jurekms/ModBusWaterMeter/src/waterMeter/timers.c

/*
 * timers.c
 *
 *  Created on: 22 wrz 2021
 *      Author: JUREK
 */


#include "timers.h"

/******************************************************************************************************************************************************
 *
 * GLOBAL VARIABLES
 *
 *******************************************************************************************************************************************************/

volatile 	TTimers			WM_TIMERS ;


/******************************************************************************************************************************************************
 *
 *initialize all timers store in WM_TIMERS GLOBAL VARIABLE
 *
 *@param	void
 *
 *@return	void
 *
 *******************************************************************************************************************************************************/

void wmTimersInit(void) {
	WM_TIMERS.LEDGreenTimer = 0;
	WM_TIMERS.LEDRedTimer = 0;
	WM_TIMERS.wmContinuousWaterFlowPeriodTimer = 0;
	WM_TIMERS.wmNoWaterFlowTimer = 0;
}
