jurekms/ModBusWaterMeter/src/waterMeter/timers.h

/*
 * timers.h
 *
 *  Created on: 22 wrz 2021
 *      Author: JUREK
 */

#ifndef SRC_WATERMETER_TIMERS_H_
#define SRC_WATERMETER_TIMERS_H_

#include <avr/pgmspace.h>


/******************************************************************************************************************************************************
 *
 * functions declarations
 *
 *******************************************************************************************************************************************************/
void wmTimersInit(void);


/******************************************************************************************************************************************************
 *
 * structure for timers, which are increment in the interrupt procedure every 10ms
 *
 *******************************************************************************************************************************************************/
typedef struct {
	uint16_t	LEDRedTimer;
	uint16_t	LEDGreenTimer;
	uint32_t	wmContinuousWaterFlowPeriodTimer;
	uint32_t	wmNoWaterFlowTimer;
} TTimers;

/******************************************************************************************************************************************************
 *
 * GLOBAL VARIABLES declarations , definitions in timers.c
 *
 *******************************************************************************************************************************************************/

extern	volatile 	TTimers			WM_TIMERS ;

#endif /* SRC_WATERMETER_TIMERS_H_ */
